megasinser/CJL/v-photos/FRONT.jpg

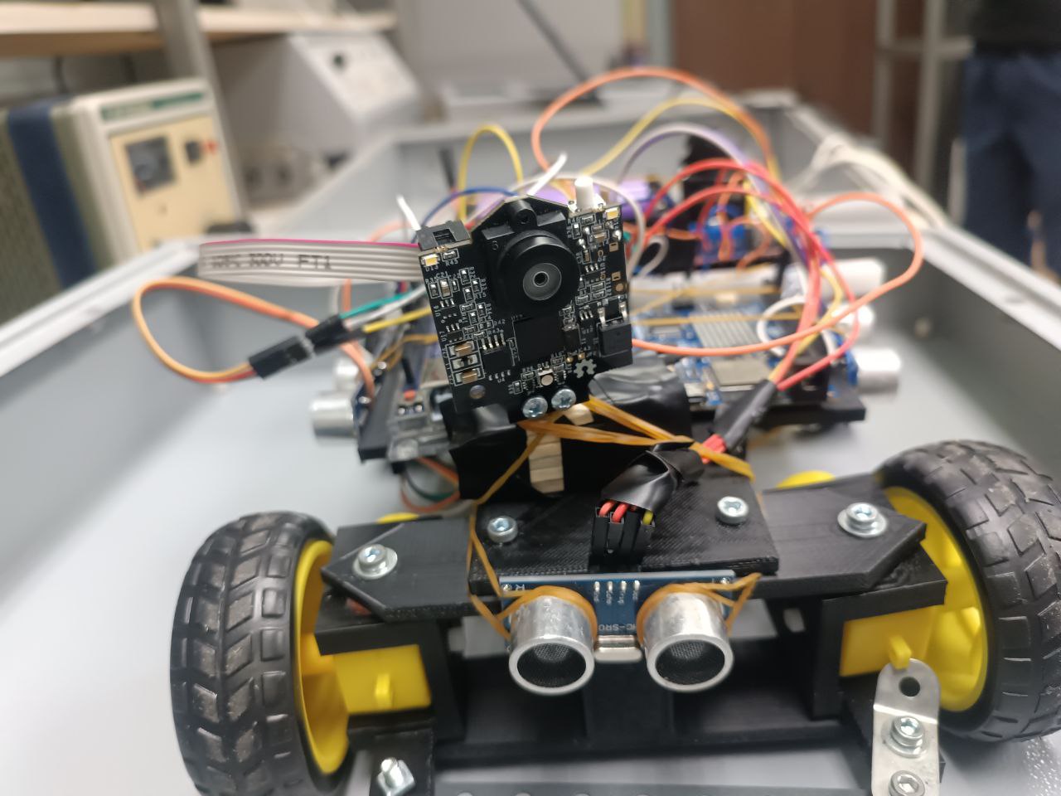
v-photos/FRONT.jpg
