megasinser/CJL/other/datasheet components/motorreductor.jpg

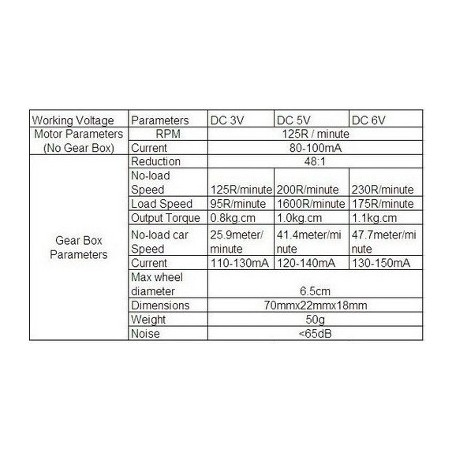
other/datasheet components/motorreductor.jpg
